Faishal-Monir/CSE-461_ParkMate-A-Robotic-Assistant-for-Parking-Cars/LAB-3/Setting up Arduino IDE in Raspberry PI.pdf

Setting Up the Arduino IDE in Raspberry PI

Before starting the interfacing experiments using arudino, ensure the Arduino IDE is properly set up on your Raspberry PI. Follow these steps:
- Download the Arduino IDE: Download the latest version of the Arduino IDE from the official website: https://www.arduino.cc/en/software
Note: Make sure to download the LINUX (Arm 64 bits) version of the IDE
- Install the IDE: Extract the files and select the install.sh file to install the IDE in your system.
Note: select Execute in Terminal during installation
- Connect the Arduino Board: Use a USB cable to connect the Arduino board to the computer.
- Select the Board and Port:
- Go to | Tools > Board | and select the appropriate Arduino board (e.g.,
Arduino Uno).
- Go to | Tools > Port | and select the COM port to which your Arduino is
connected.
This setup ensures that the connected Arduino board is ready for programming and interfacing with external components.
- Run an sample sketch to verify the installation:
- Select | Files > Examples > 01. Basics > Blink | and Upload
the sketch.
- Once the upload is done, check whether the onboard led is blinking or not.
