Faishal-Monir/CSE-461_ParkMate-A-Robotic-Assistant-for-Parking-Cars/LAB-5/Black and White Zone.pdf

## Lab Worksheet 5

CSE461: Introduction to Robotics
Department of Computer Science and Engineering

Lab 05: Interfacing Arduino and Raspberry Pi using UART Protocol to Display IR Sensor Values on an I2C LCD

Black and White Zones
