Faishal-Monir/CSE-461_ParkMate-A-Robotic-Assistant-for-Parking-Cars/LAB-1/IMG_20251023_152306.jpg

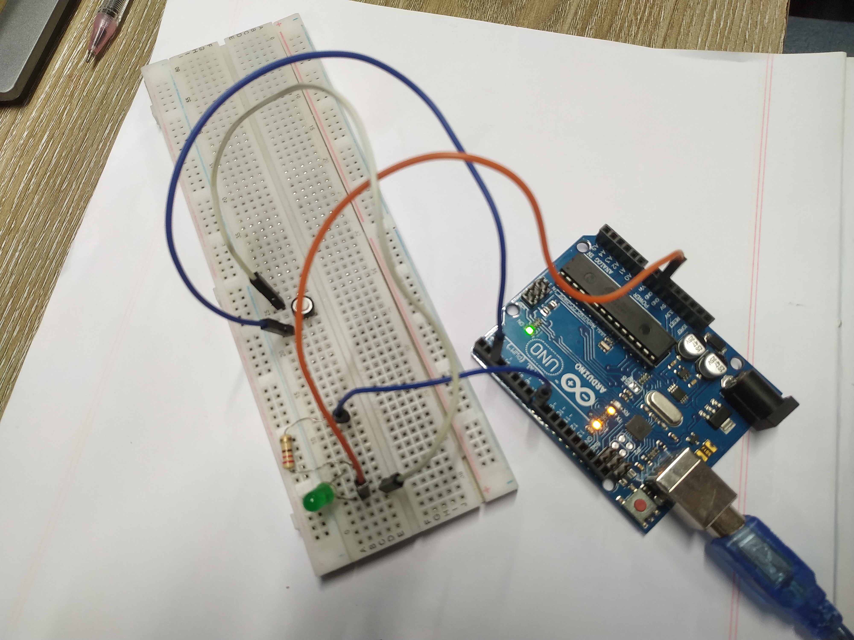
LAB-1/IMG_20251023_152306.jpg
