Faishal-Monir/CSE-461_ParkMate-A-Robotic-Assistant-for-Parking-Cars/LAB-4/1763631137168.jpg

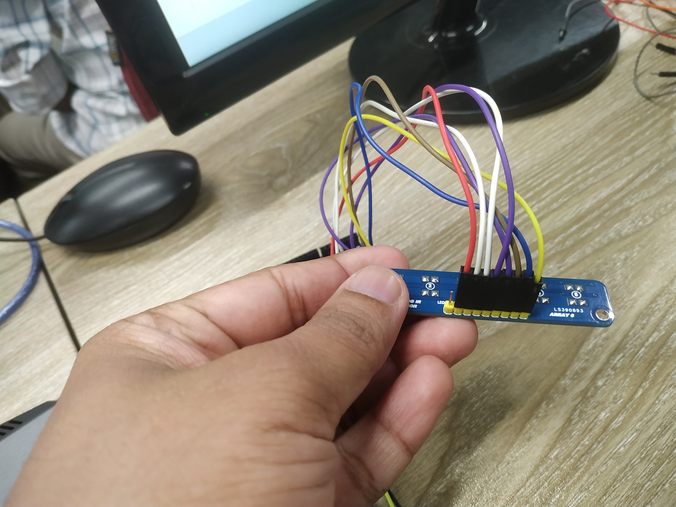
LAB-4/1763631137168.jpg
