Faishal-Monir/CSE-461_ParkMate-A-Robotic-Assistant-for-Parking-Cars/LAB-4/IMG_20251120_144909.jpg

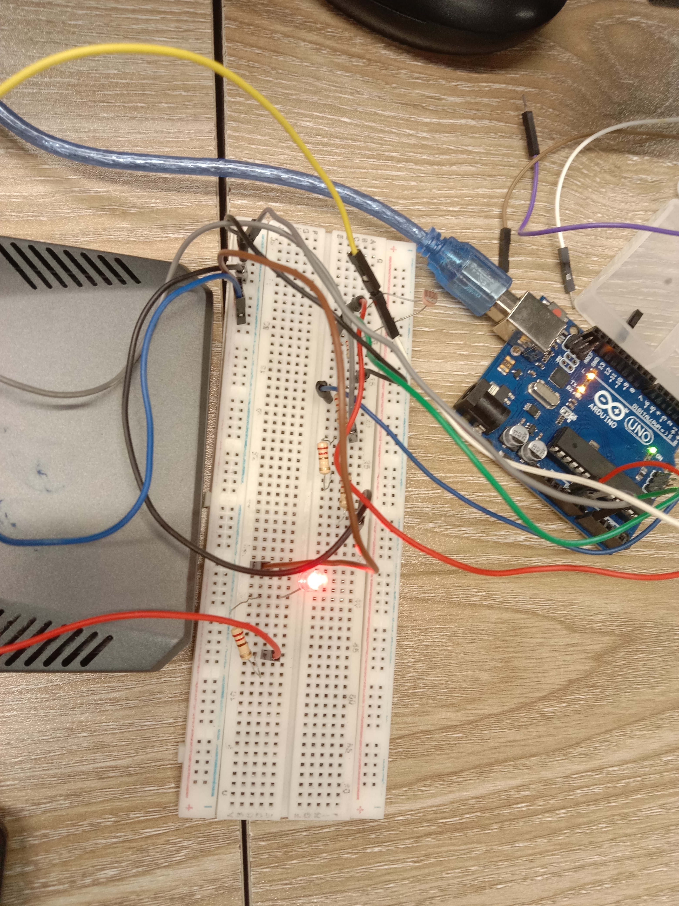
LAB-4/IMG_20251120_144909.jpg
